Positronic-IO/air-hockey/notebooks/homography/homography_4.jpg

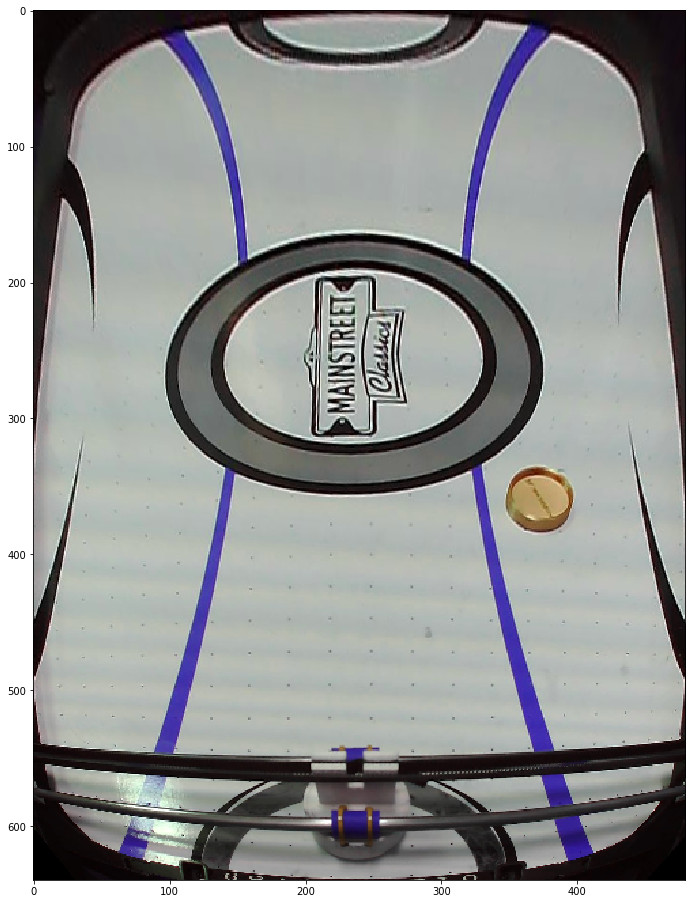
notebooks/homography/homography_4.jpg
