Positronic-IO/air-hockey/notebooks/homography/homography_bot_red.jpg

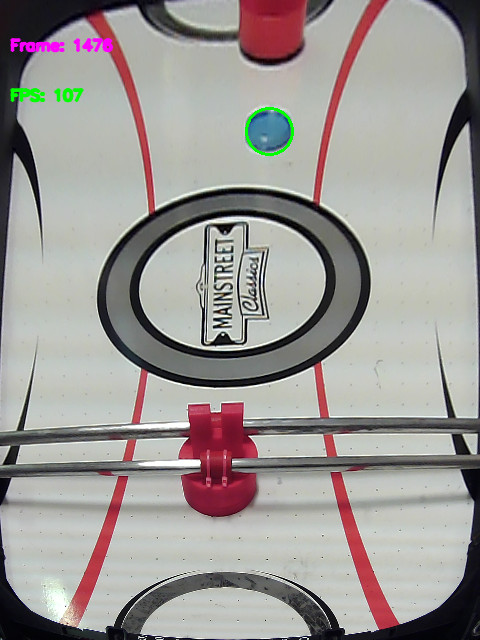
notebooks/homography/homography_bot_red.jpg
