Positronic-IO/air-hockey/3DParts/bushings.stl

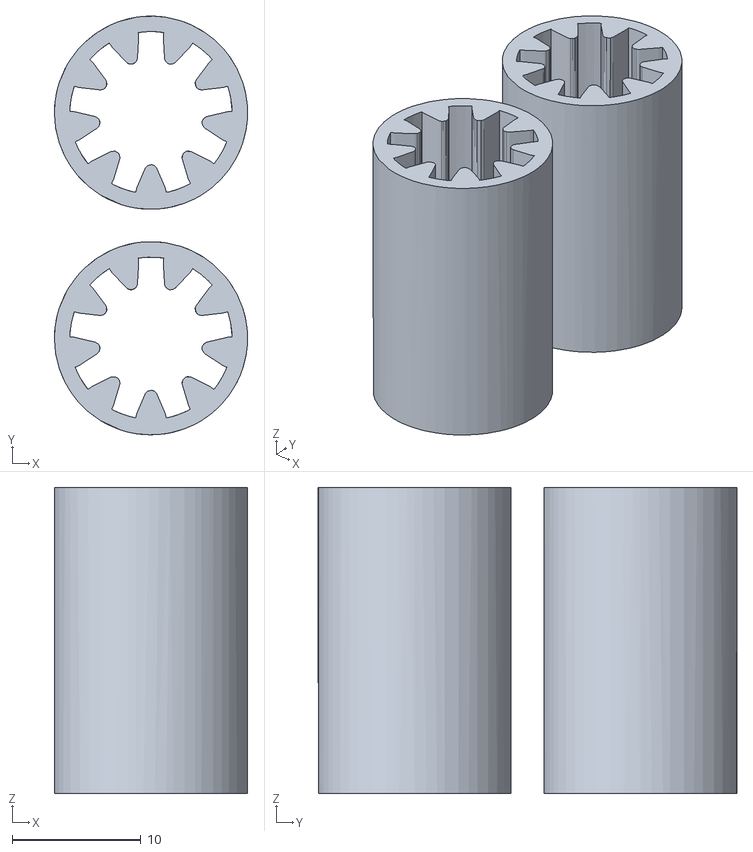
[picture p20: CAD file, 2019-03-21]
3DParts/bushings.stl
15.0 x 32.5 x 23.8
